TomNisbet/nqsap-pcb/docs/assets/images/ab-registers-board-v10-500.jpg

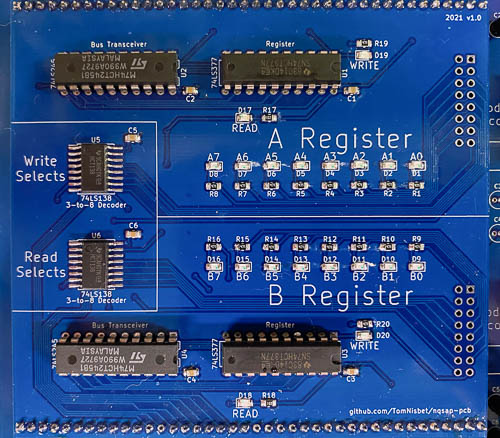
docs/assets/images/ab-registers-board-v10-500.jpg
