TomNisbet/nqsap-pcb/docs/assets/images/backplane-board.jpg

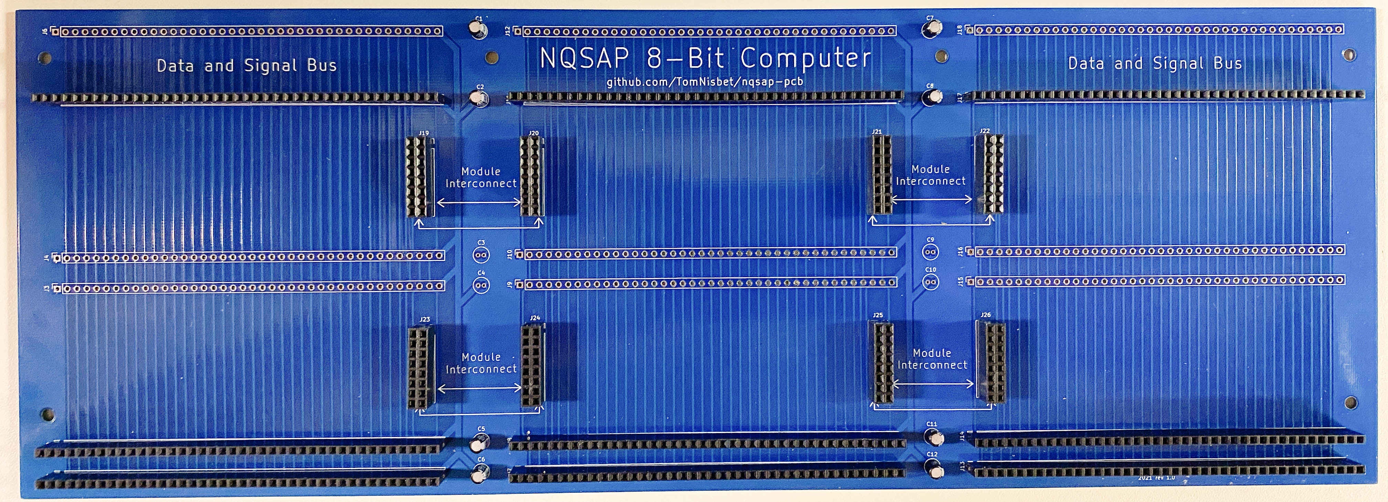
docs/assets/images/backplane-board.jpg
