TomNisbet/nqsap-pcb/docs/assets/images/boards1.jpg

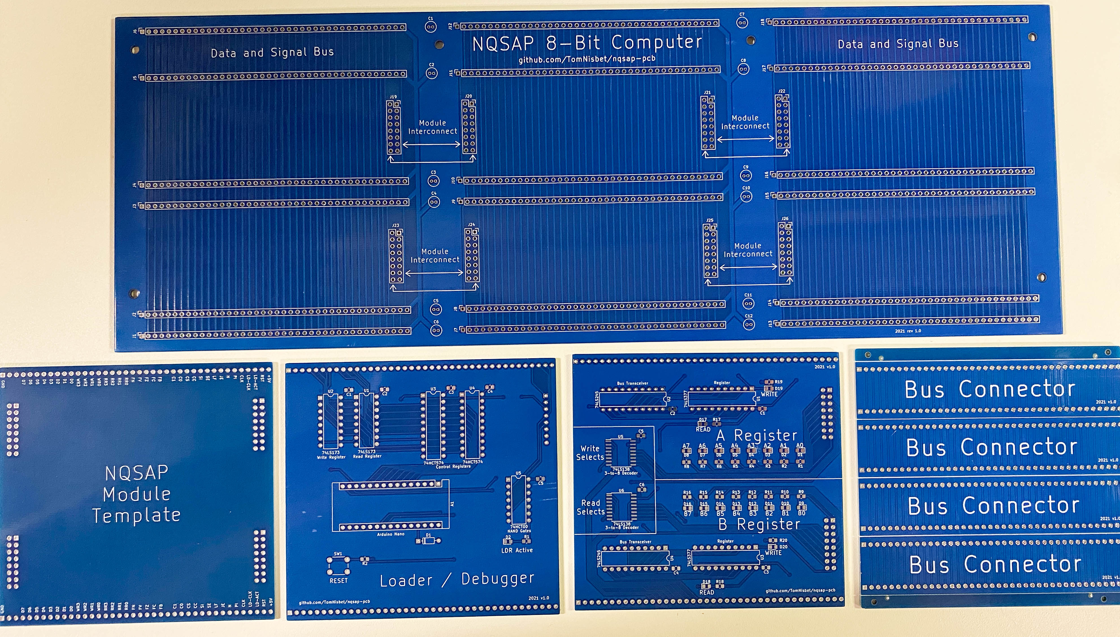
docs/assets/images/boards1.jpg
