TomNisbet/nqsap-pcb/docs/assets/images/boards1a-500.jpg

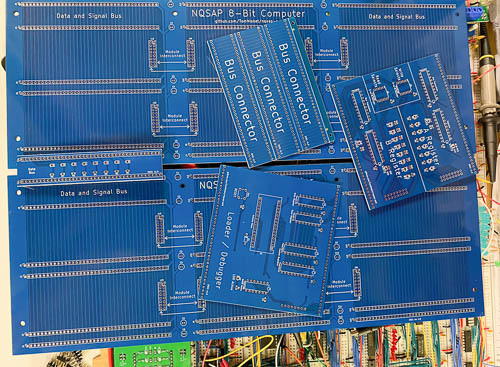
docs/assets/images/boards1a-500.jpg
