TomNisbet/nqsap-pcb/docs/assets/images/boards1b-500.jpg

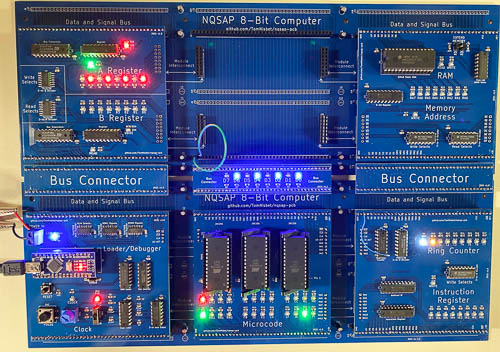
docs/assets/images/boards1b-500.jpg
