TomNisbet/nqsap-pcb/docs/assets/images/boards2.jpg

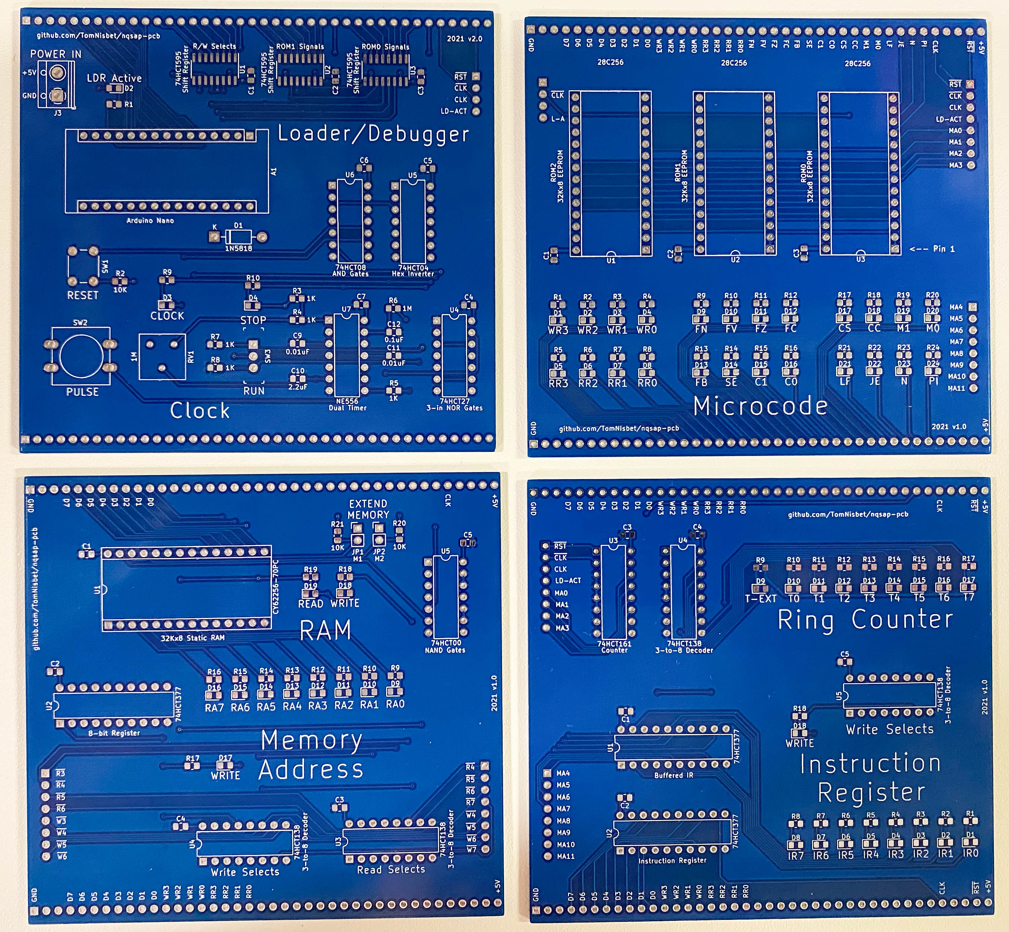
docs/assets/images/boards2.jpg
