TomNisbet/nqsap-pcb/docs/assets/images/boards3.jpg

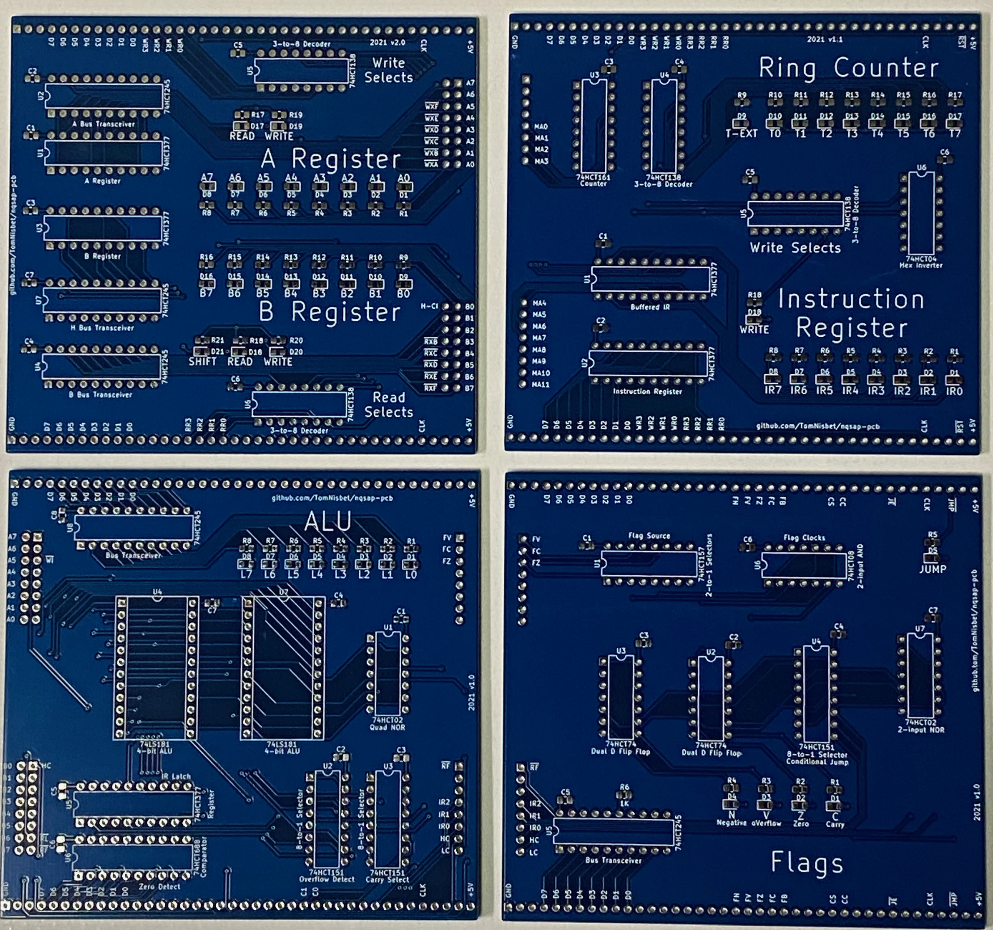
docs/assets/images/boards3.jpg
