TomNisbet/nqsap-pcb/docs/assets/images/boards4.jpg

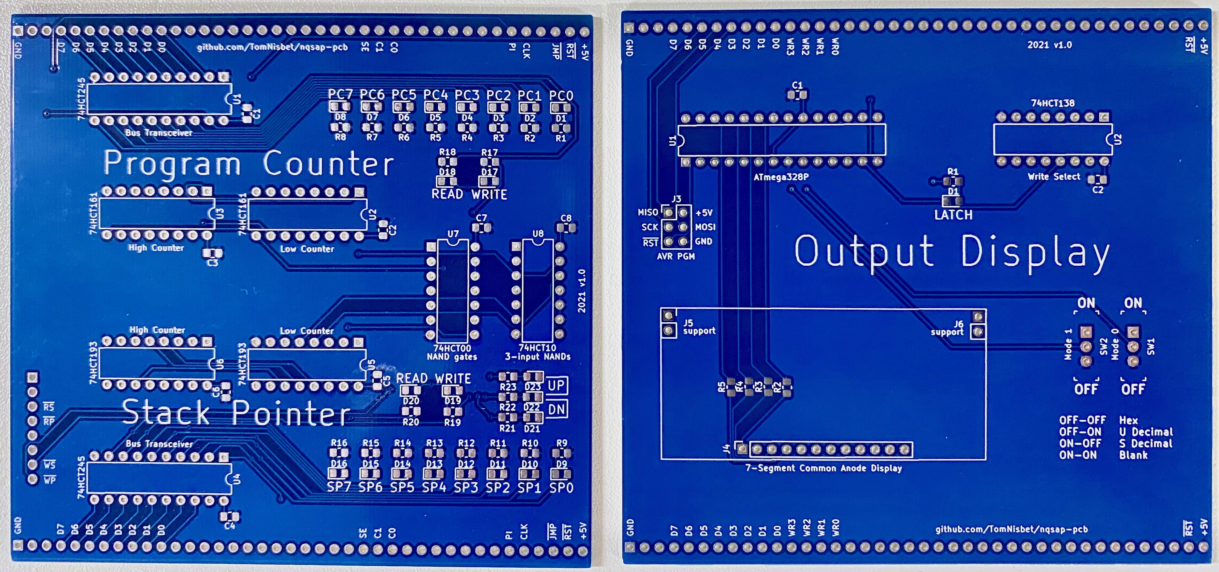
docs/assets/images/boards4.jpg
