TomNisbet/nqsap-pcb/docs/assets/images/boards5.jpg

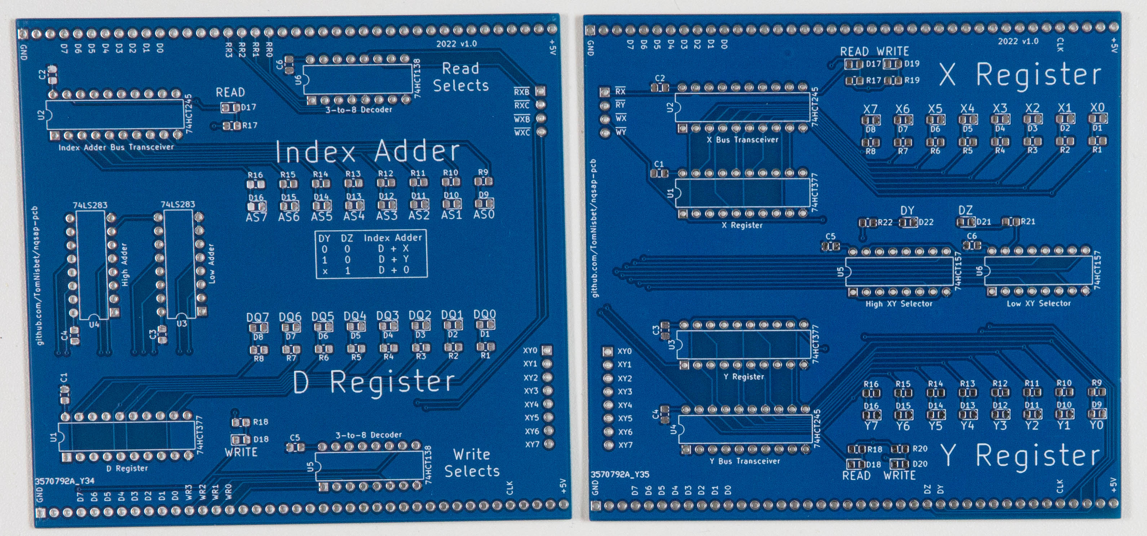
docs/assets/images/boards5.jpg
