TomNisbet/nqsap-pcb/docs/assets/images/IMG_6680-500.jpg

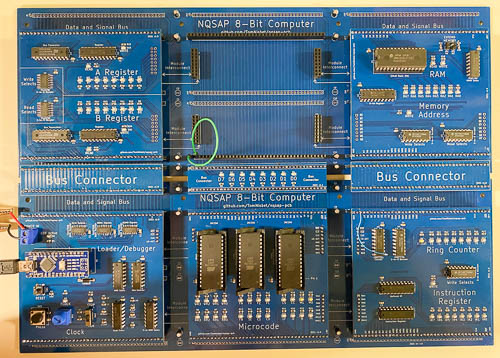
docs/assets/images/IMG_6680-500.jpg
