TomNisbet/nqsap-pcb/docs/assets/images/ir-rc-board-v10-500.jpg

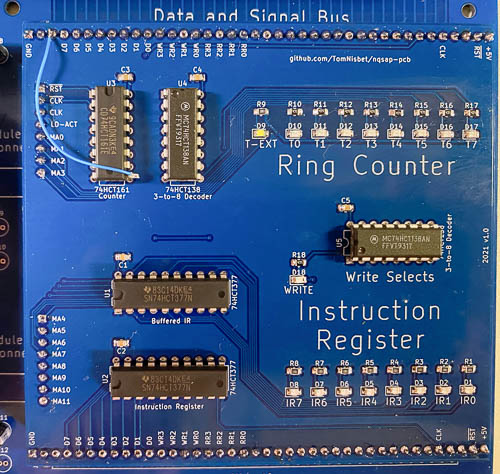
docs/assets/images/ir-rc-board-v10-500.jpg
