TomNisbet/nqsap-pcb/docs/assets/images/nqsap-pcb-500.jpg

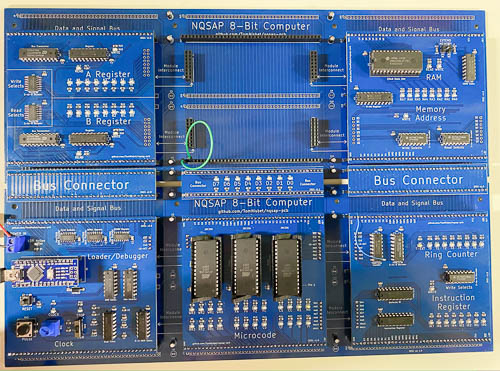
docs/assets/images/nqsap-pcb-500.jpg
