TomNisbet/nqsap-pcb/docs/assets/images/select-interconnect.jpg

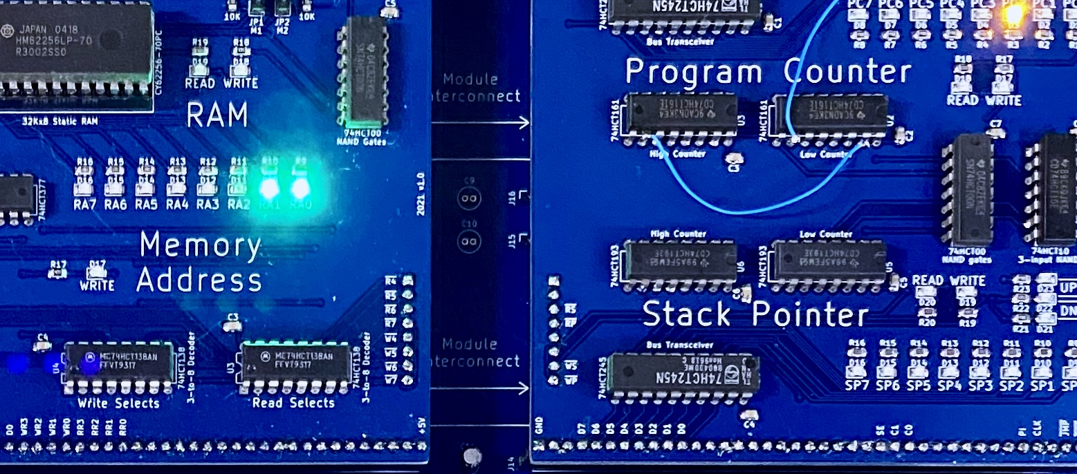
docs/assets/images/select-interconnect.jpg
