TomNisbet/nqsap-pcb/NQSAP PCB schematics/bus-connect-front.png

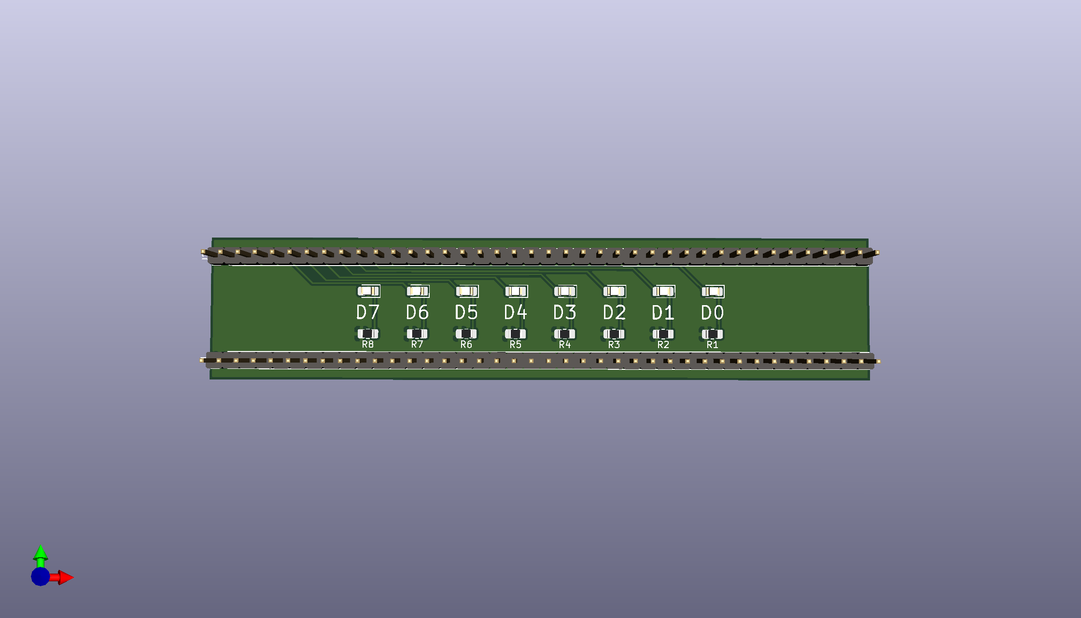
NQSAP PCB schematics/bus-connect-front.png
