TomNisbet/nqsap-pcb/NQSAP PCB schematics/bus-connect.png

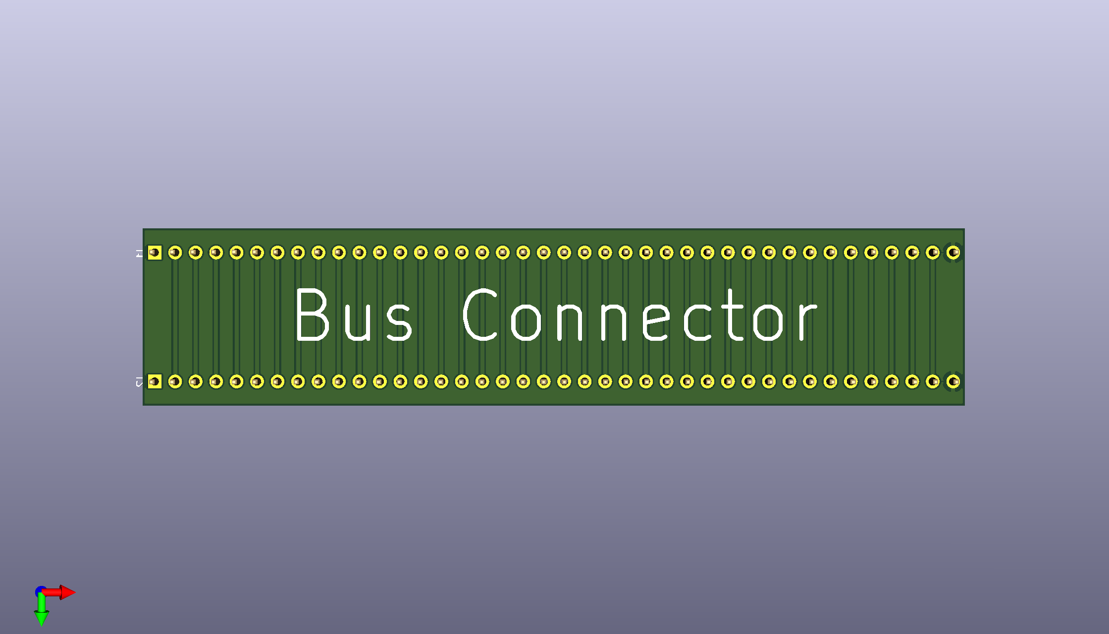
NQSAP PCB schematics/bus-connect.png
