TomNisbet/nqsap-pcb/docs/assets/images/build3-500.jpg

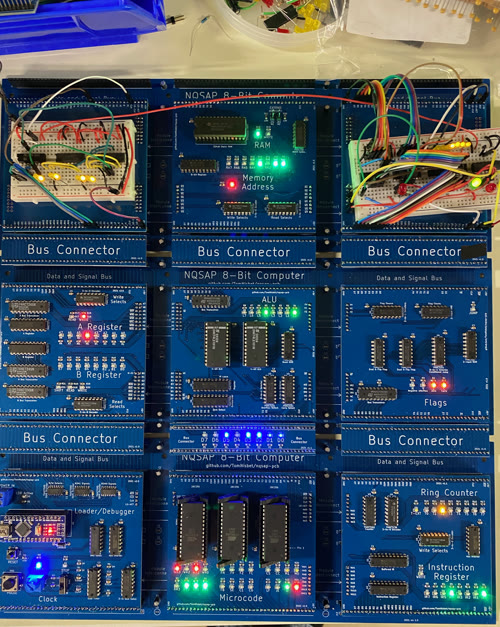
docs/assets/images/build3-500.jpg
