TomNisbet/nqsap-pcb/NQSAP PCB schematics/microcode/microcode.kicad_pcb

## KiCad design NQSAP PCB schematics/microcode/microcode.kicad_pcb (2021-10-31)

Schematic: microcode.sch, NQSAP-PCB Microcode ROMs

Parts:
C1, C2, C3: 0.1uF; C_0805_2012Metric_Pad1.18x1.45mm_HandSolder
D1: WR3; LED_0805_2012Metric_Pad1.15x1.40mm_HandSolder
D2: WR2; LED_0805_2012Metric_Pad1.15x1.40mm_HandSolder
D3: WR1; LED_0805_2012Metric_Pad1.15x1.40mm_HandSolder
D4: WR0; LED_0805_2012Metric_Pad1.15x1.40mm_HandSolder
D5: RR3; LED_0805_2012Metric_Pad1.15x1.40mm_HandSolder
D6: RR2; LED_0805_2012Metric_Pad1.15x1.40mm_HandSolder
D7: RR1; LED_0805_2012Metric_Pad1.15x1.40mm_HandSolder
D8: RR0; LED_0805_2012Metric_Pad1.15x1.40mm_HandSolder
D9: FN; LED_0805_2012Metric_Pad1.15x1.40mm_HandSolder
D10: FV; LED_0805_2012Metric_Pad1.15x1.40mm_HandSolder
D11: FZ; LED_0805_2012Metric_Pad1.15x1.40mm_HandSolder
D12: FC; LED_0805_2012Metric_Pad1.15x1.40mm_HandSolder
D13: FB; LED_0805_2012Metric_Pad1.15x1.40mm_HandSolder
D14: SE; LED_0805_2012Metric_Pad1.15x1.40mm_HandSolder
D15: C1; LED_0805_2012Metric_Pad1.15x1.40mm_HandSolder
D16: C0; LED_0805_2012Metric_Pad1.15x1.40mm_HandSolder
D17: CS; LED_0805_2012Metric_Pad1.15x1.40mm_HandSolder
D18: CC; LED_0805_2012Metric_Pad1.15x1.40mm_HandSolder
D19: M1; LED_0805_2012Metric_Pad1.15x1.40mm_HandSolder
D20: M0; LED_0805_2012Metric_Pad1.15x1.40mm_HandSolder
D21: LF; LED_0805_2012Metric_Pad1.15x1.40mm_HandSolder
D22: JE; LED_0805_2012Metric_Pad1.15x1.40mm_HandSolder
D23: N; LED_0805_2012Metric_Pad1.15x1.40mm_HandSolder
D24: PI; LED_0805_2012Metric_Pad1.15x1.40mm_HandSolder
J1, J2: Bus; PinHeader_1x40_P2.54mm_Vertical
J3: IC-LT; PinHeader_1x04_P2.54mm_Vertical
J5: IC-RT; PinHeader_1x08_P2.54mm_Vertical
J6: IC-RB; PinHeader_1x08_P2.54mm_Vertical
R1, R2, R3, R4, R22, R24: R_RED; R_0805_2012Metric_Pad1.20x1.40mm_HandSolder
R5, R6, R7, R8: R_GRN; R_0805_2012Metric_Pad1.20x1.40mm_HandSolder
R9, R10, R11, R12, R17, R18: R_BLUE; R_0805_2012Metric_Pad1.20x1.40mm_HandSolder
R13, R15, R16, R19, R20, R21, R23: R_YEL; R_0805_2012Metric_Pad1.20x1.40mm_HandSolder
R14: R_WHT; R_0805_2012Metric_Pad1.20x1.40mm_HandSolder
U1, U2, U3: 28C256; DIP-28_W15.24mm_Socket

Connections:
+5V: C1.2, C2.2, C3.2, J1.40, J2.40, U1.1 (A14), U1.27 (~WE), U1.28 (VCC), U2.26 (A13), U2.27 (~WE), U2.28 (VCC), U3.27 (~WE), U3.28 (VCC)
C0: D16.2 (A), J1.27, J2.27, U2.11 (D0)
C1: D15.2 (A), J1.26, J2.26, U2.12 (D1)
CC: D18.2 (A), J1.29, J2.29, U3.18 (D6)
CLK: J1.36, J5.3
CS: D17.2 (A), J1.28, J2.28, U3.19 (D7)
FB: D13.2 (A), J1.24, J2.24, U2.15 (D3)
FC: D12.2 (A), J1.23, J2.23, U2.16 (D4)
FN: D9.2 (A), J1.20, J2.20, U2.19 (D7)
FV: D10.2 (A), J1.21, J2.21, U2.18 (D6)
FZ: D11.2 (A), J1.22, J2.22, U2.17 (D5)
GND: C1.1, C2.1, C3.1, J1.1, J2.1, R1.2, R2.2, R3.2, R4.2, R5.2, R6.2, R7.2, R8.2, R9.2, R10.2, R11.2, R12.2, R13.2, R14.2, R15.2, R16.2, R17.2, R18.2, R19.2, R20.2, R21.2, R22.2, R23.2, R24.2, U1.2 (A12), U1.14 (GND), U1.20 (~CS), U1.26 (A13), U2.1 (A14), U2.2 (A12), U2.14 (GND), U2.20 (~CS), U3.1 (A14), U3.2 (A12), U3.14 (GND), U3.20 (~CS), U3.26 (A13)
JE: D22.2 (A), J1.33, J2.33, U3.13 (D2)
LD-ACT: J3.4, J5.4, U1.22 (~OE), U2.22 (~OE), U3.22 (~OE)
LF: D21.2 (A), J1.32, J2.32, U3.15 (D3)
M0: D20.2 (A), J1.31, J2.31, U3.16 (D4)
M1: D19.2 (A), J1.30, J2.30, U3.17 (D5)
MA0: J5.5, U1.10 (A0), U2.10 (A0), U3.10 (A0)
MA1: J5.6, U1.9 (A1), U2.9 (A1), U3.9 (A1)
MA2: J5.7, U1.8 (A2), U2.8 (A2), U3.8 (A2)
MA3: J5.8, U1.7 (A3), U2.7 (A3), U3.7 (A3)
MA4: J6.1, U1.6 (A4), U2.6 (A4), U3.6 (A4)
MA5: J6.2, U1.5 (A5), U2.5 (A5), U3.5 (A5)
MA6: J6.3, U1.4 (A6), U2.4 (A6), U3.4 (A6)
MA7: J6.4, U1.3 (A7), U2.3 (A7), U3.3 (A7)
MA8: J6.5, U1.25 (A8), U2.25 (A8), U3.25 (A8)
MA9: J6.6, U1.24 (A9), U2.24 (A9), U3.24 (A9)
MA10: J6.7, U1.21 (A10), U2.21 (A10), U3.21 (A10)
MA11: J6.8, U1.23 (A11), U2.23 (A11), U3.23 (A11)
N: D23.2 (A), J1.34, J2.34, U3.12 (D1)
unnamed: D1.1 (K), R1.1
unnamed: D2.1 (K), R2.1
unnamed: D3.1 (K), R3.1
unnamed: D4.1 (K), R4.1
unnamed: D5.1 (K), R5.1
unnamed: D6.1 (K), R6.1
unnamed: D7.1 (K), R7.1
unnamed: D8.1 (K), R8.1
unnamed: D9.1 (K), R9.1
unnamed: D10.1 (K), R10.1
unnamed: D11.1 (K), R11.1
unnamed: D12.1 (K), R12.1
unnamed: D13.1 (K), R13.1
unnamed: D14.1 (K), R14.1
unnamed: D15.1 (K), R15.1
unnamed: D16.1 (K), R16.1
unnamed: D17.1 (K), R17.1
unnamed: D18.1 (K), R18.1
unnamed: D19.1 (K), R19.1
unnamed: D20.1 (K), R20.1
unnamed: D21.1 (K), R21.1
unnamed: D22.1 (K), R22.1
unnamed: D23.1 (K), R23.1
unnamed: D24.1 (K), R24.1
PI: D24.2 (A), J1.35, J2.35, U3.11 (D0)
RR0: D8.2 (A), J1.19, J2.19, U1.11 (D0)
RR1: D7.2 (A), J1.18, J2.18, U1.12 (D1)
RR2: D6.2 (A), J1.17, J2.17, U1.13 (D2)
RR3: D5.2 (A), J1.16, J2.16, U1.15 (D3)
SE: D14.2 (A), J1.25, J2.25, U2.13 (D2)
WR0: D4.2 (A), J1.15, J2.15, U1.16 (D4)
WR1: D3.2 (A), J1.14, J2.14, U1.17 (D5)
WR2: D2.2 (A), J1.13, J2.13, U1.18 (D6)
WR3: D1.2 (A), J1.12, J2.12, U1.19 (D7)
~CLK: J3.2, J5.2
~RST: J1.39, J5.1

Notes on the sheet:
ROM2
ROM1
ROM0
MICROCODE ROMS

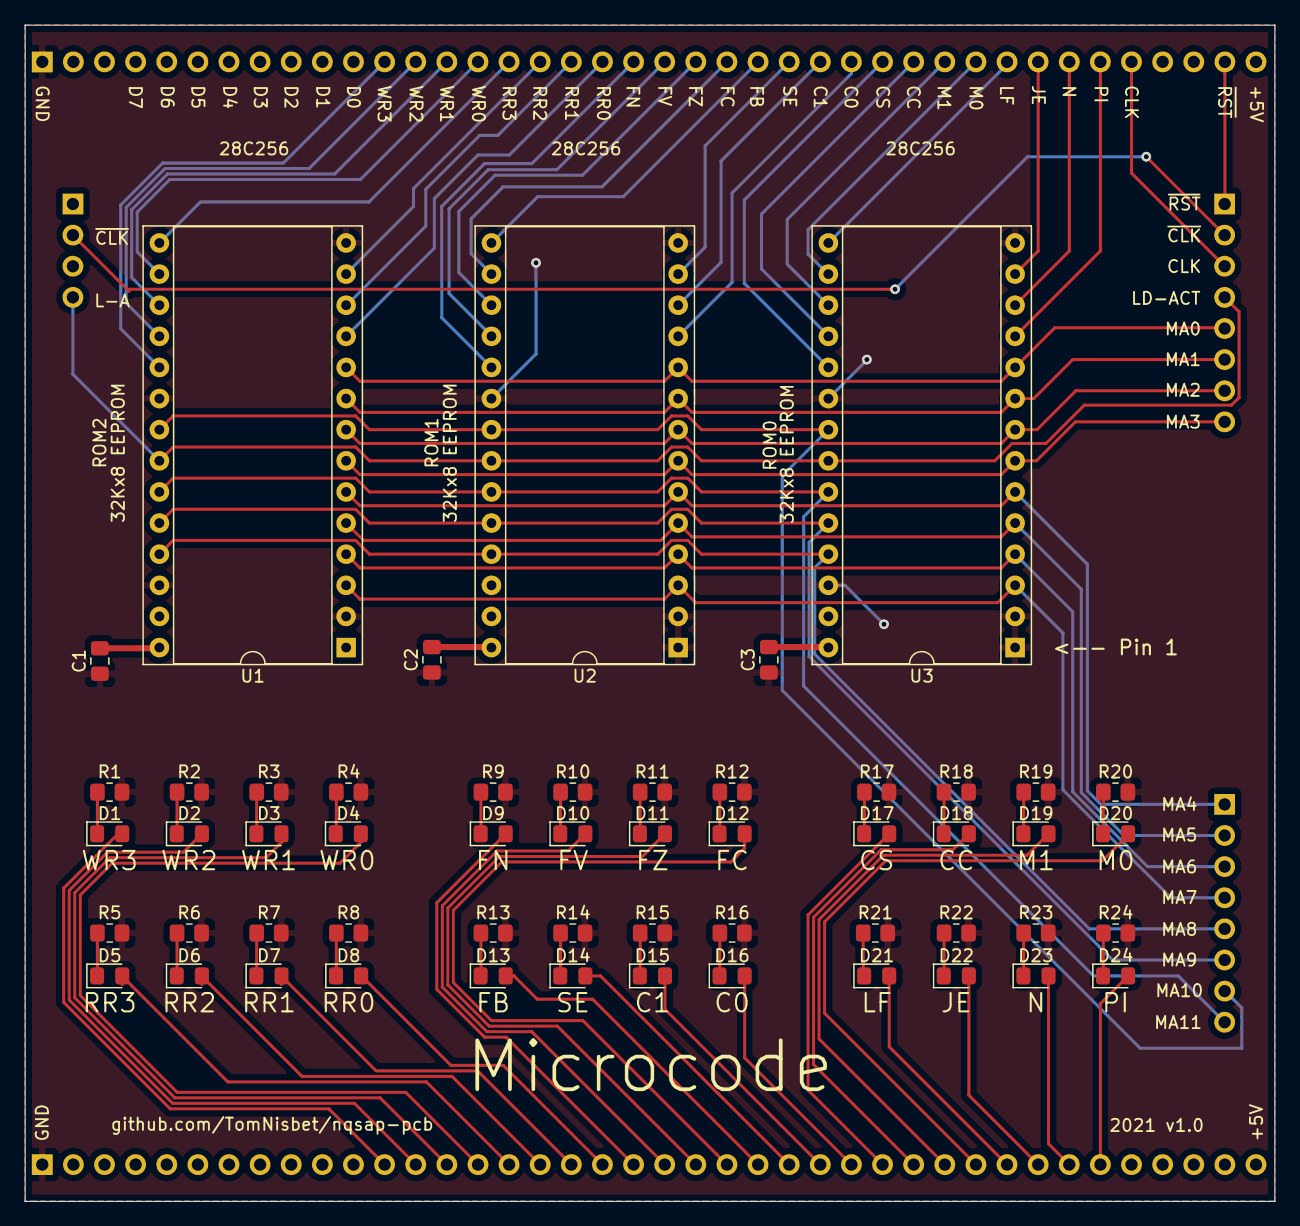
[picture p95: board microcode.kicad_pcb from above]

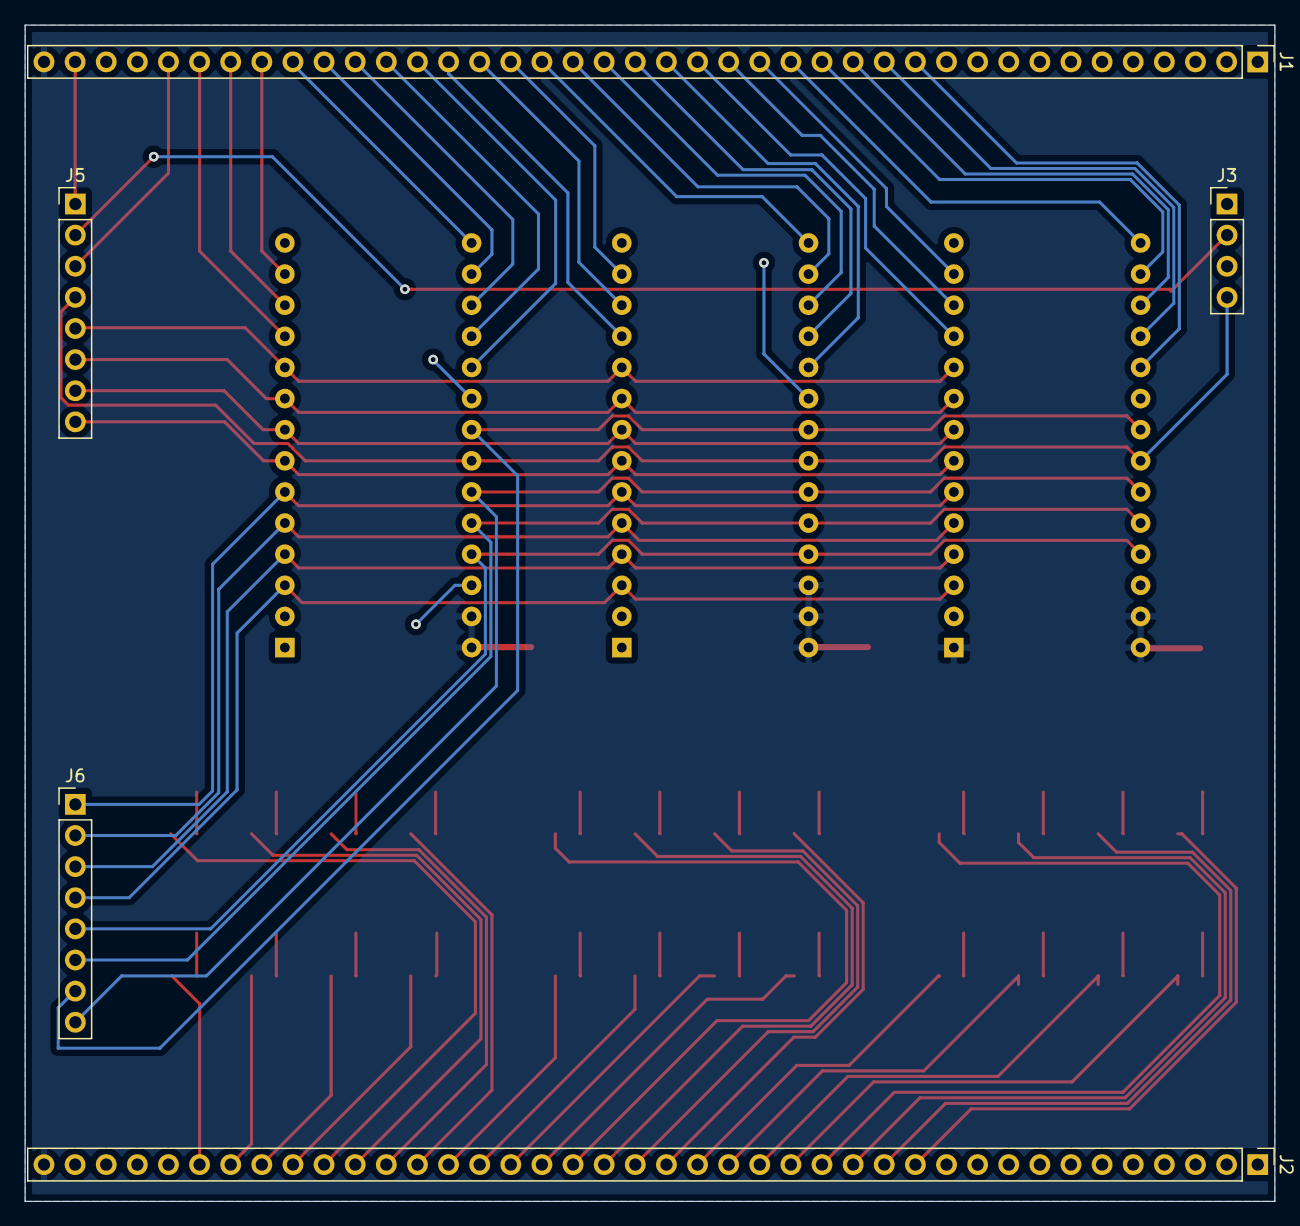
[picture p96: board microcode.kicad_pcb from below]

Board: 2 copper layers, 102.0 x 96.0 mm, 59 parts (5 on the bottom side), 66 nets.
